andrewmv/climate-controller/Enclosure/7-segment_layout.png

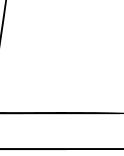
Enclosure/7-segment_layout.png
