andrewmv/climate-controller/Enclosure/Screenshot from 2021-05-04 10-55-42.png

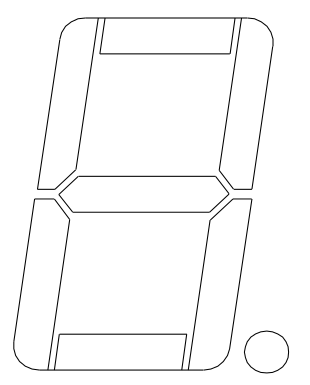
Enclosure/Screenshot from 2021-05-04 10-55-42.png
