andrewmv/climate-controller/Enclosure/7-segment_diffuser_test.stl

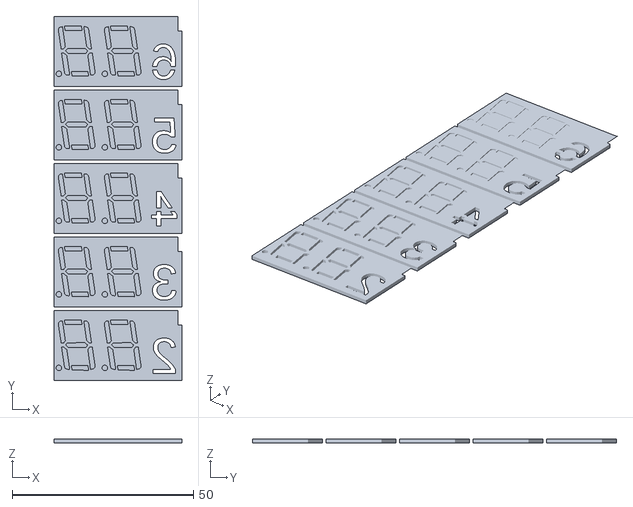
[picture p28: CAD file, 2021-05-17]
Enclosure/7-segment_diffuser_test.stl
35.2 x 100.5 x 1.00
