andrewmv/climate-controller/Enclosure/7-segment_layout_scaled.dxf

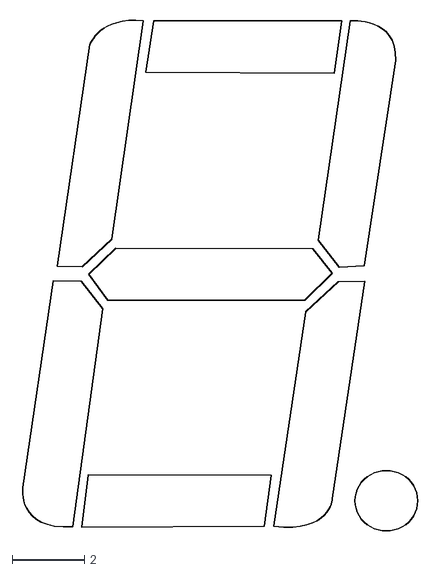
[picture p29: CAD file, 2021-05-17]
Enclosure/7-segment_layout_scaled.dxf
11.1 x 14.3
